KBieszczad/Bike-Computer/software/include/Bitmaps.h

#pragma once
#include <U8g2lib.h>
// lopaka
static const unsigned char image_battery_10_bits[] U8X8_PROGMEM = {0x00,0x00,0x00,0x00,0x00,0xfc,0xff,0x1f,0x00,0x00,0x00,0x00,0x00,0x02,0x00,0x20,0x01,0x00,0x00,0x00,0x00,0x02,0x00,0x28,0x00,0x00,0x00,0x00,0x80,0x03,0x00,0x28,0x10,0x00,0x00,0x00,0x40,0x00,0x00,0x28,0x00,0x00,0x00,0x00,0x40,0x00,0x00,0x28,0x00,0x00,0x00,0x00,0x40,0x00,0x00,0x28,0x00,0x00,0x00,0x00,0x40,0x00,0x00,0x28,0x00,0x00,0x00,0x00,0x40,0x00,0x00,0x28,0x00,0x00,0x00,0x00,0x80,0x03,0x00,0x28,0x00,0x00,0x00,0x00,0x00,0x02,0x00,0x28,0x00,0x00,0x00,0x00,0x00,0x02,0x00,0x20,0x00,0x00,0x00,0x00,0x00,0xfc,0xff,0x1f};
static const unsigned char image_battery_33_bits[] U8X8_PROGMEM = {0x00,0x00,0x00,0xf0,0xff,0x7f,0x08,0x00,0x80,0x08,0x00,0xb6,0x0e,0x00,0xb6,0x01,0x00,0xb6,0x01,0x00,0xb6,0x01,0x00,0xb6,0x01,0x00,0xb6,0x01,0x00,0xb6,0x0e,0x00,0xb6,0x08,0x00,0xb6,0x08,0x00,0x80,0xf0,0xff,0x7f,0x00,0x00,0x00,0x00,0x00,0x00};
static const unsigned char image_battery_67_bits[] U8X8_PROGMEM = {0x00,0x00,0x00,0xf0,0xff,0x7f,0x08,0x00,0x80,0x08,0xd8,0xb6,0x0e,0xd8,0xb6,0x01,0xd8,0xb6,0x01,0xd8,0xb6,0x01,0xd8,0xb6,0x01,0xd8,0xb6,0x01,0xd8,0xb6,0x0e,0xd8,0xb6,0x08,0xd8,0xb6,0x08,0x00,0x80,0xf0,0xff,0x7f,0x00,0x00,0x00,0x00,0x00,0x00};
static const unsigned char image_battery_100_bits[] U8X8_PROGMEM = {0x00,0x00,0x00,0xf0,0xff,0x7f,0x08,0x00,0x80,0xa8,0xaa,0xaa,0xae,0xaa,0xaa,0xa1,0xaa,0xaa,0xa1,0xaa,0xaa,0xa1,0xaa,0xaa,0xa1,0xaa,0xaa,0xa1,0xaa,0xaa,0xae,0xaa,0xaa,0xa8,0xaa,0xaa,0x08,0x00,0x80,0xf0,0xff,0x7f,0x00,0x00,0x00,0x00,0x00,0x00};
static const unsigned char image_crossed_bits[] U8X8_PROGMEM = {0x00,0x00,0x00,0x00,0x03,0x06,0x07,0x07,0x8e,0x03,0xdc,0x01,0xf8,0x00,0x70,0x00,0xf8,0x00,0xdc,0x01,0x8e,0x03,0x07,0x07,0x03,0x06,0x00,0x00,0x00,0x00,0x00,0x00};
static const unsigned char image_checked_bits[] U8X8_PROGMEM = {0x00,0x00,0x00,0x00,0x00,0x00,0x00,0x20,0x00,0x30,0x00,0x38,0x01,0x1c,0x03,0x0e,0x07,0x07,0x8e,0x03,0xdc,0x01,0xf8,0x00,0x70,0x00,0x20,0x00,0x00,0x00,0x00,0x00};
